pdsmart/MZ80A_80COLOUR/docs/IMG_9789.jpg

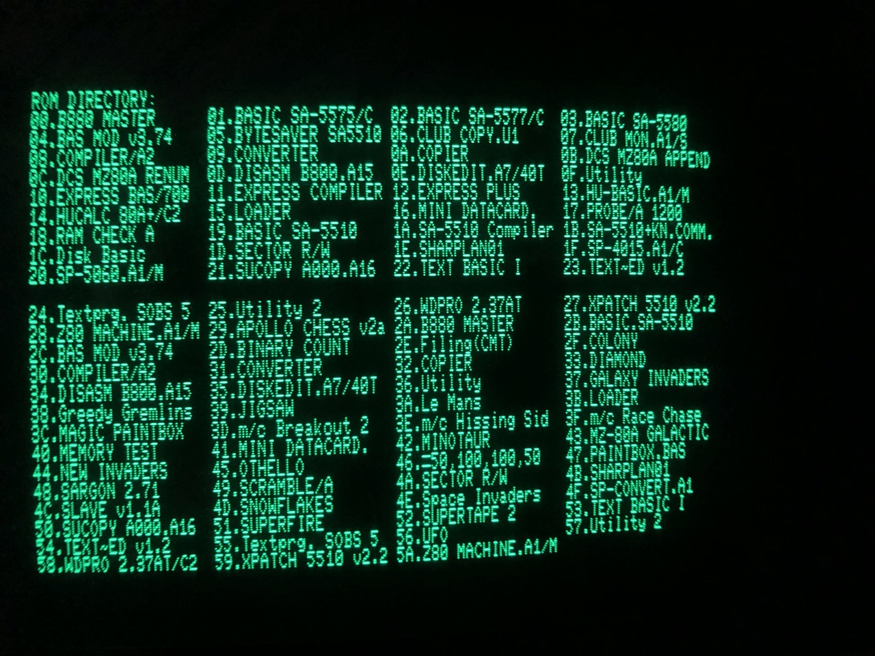
docs/IMG_9789.jpg
