pdsmart/MZ80A_80COLOUR/docs/IMG_9790.jpg

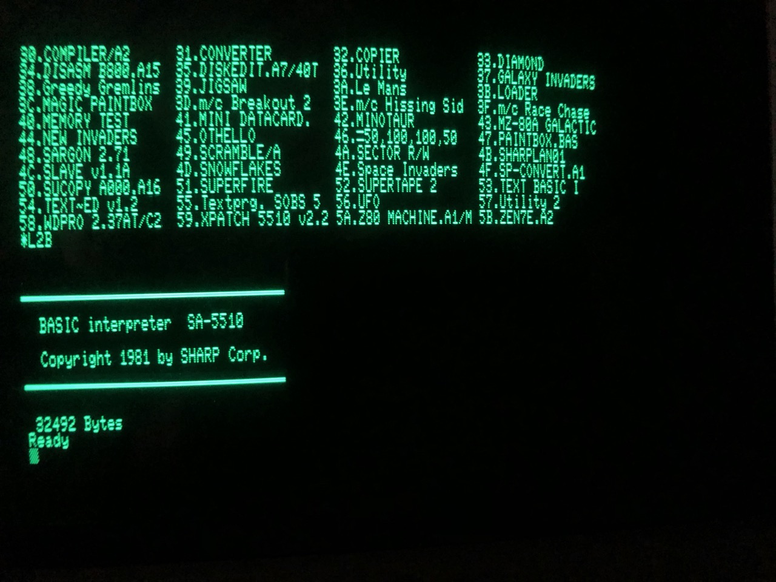
docs/IMG_9790.jpg
